cheehieu/recall/hw/docs/BLE/nRF52 Development Kit - Hardware files 1_1_1/PCA64110-NFC antenna flexprint 1_0_0/Production files/GERBER/400148_PCB_Laminate_Specification.pdf

### PCB Laminate Specification

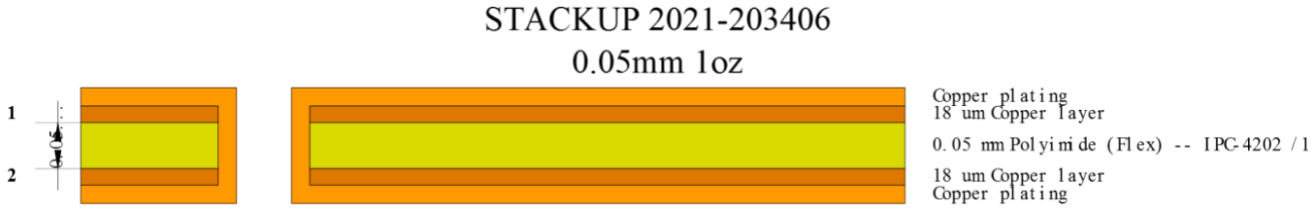
[picture p5: figure]

Page 1 of 1 | Rev. 1.0.0, 2016-03-10

PCB laminate parameters

PCB code | 4000148
Number of copper layers | 2 layers
Laminate material | FR4
Total board thickness | 0.05mm
PCB stackup | See Figure 1
Copper thickness | See Figure 1
Surface finish | Lead-Free HASL
Compliance with environmental directives | RoHS

Table 1: PCB substrate details

The PCB layer stackup order (from top layer and down) shall be as follows with reference to the Gerber file extensions given below:

- Top layer: | .GTL
- Bottom layer: | .GBL

Stackup

Figure 1: Elprint's 2 layer 2021-203406 stackup
