cheehieu/recall/docs/reminder.pdf

Product: Reminder

- All hardware
- Water proof
- Stupid cheap

Components:

- Transparent Silicon Rubber Button
- 555 timer or equivalent
- Low power LED
- Watch battery
- Sticky tape for mounting

Usage:

- Press button and an LED blinks lighting up button
- Blinks for 30 minutes or until pressed again
- Stick around the house, shower, etc.

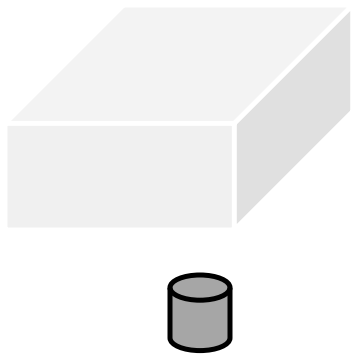
[picture p6: figure]

Silicon transparent button

Toggle button switch

Timer (and capacitor)

Low energy LEDs (on if bright enough)

Watch battery

Back plate

Sticky tape

Before press

After press for up to 30 minutes blinking
