cheehieu/recall/mech/recall_clip/recall_clip_male.step

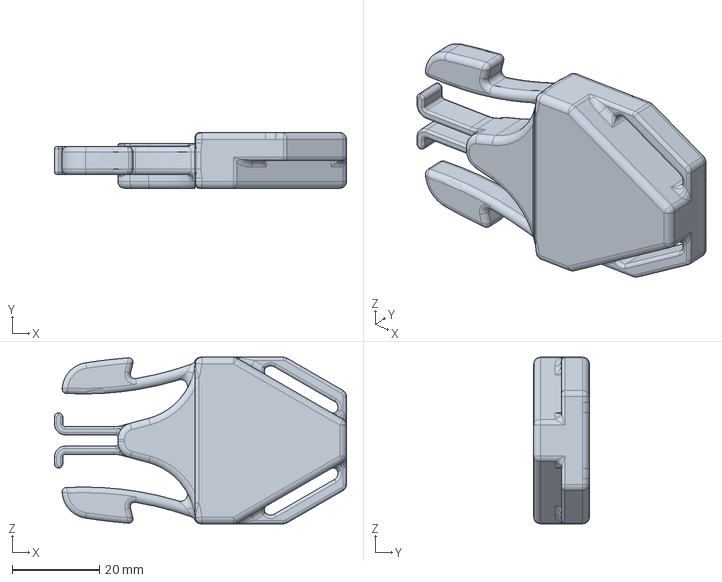
[picture p21: CAD file, 2016-09-16]
mech/recall_clip/recall_clip_male.step
66.8 x 12.7 x 38.1 mm
