cheehieu/recall/mech/recall_clip/bg_clip_female.step

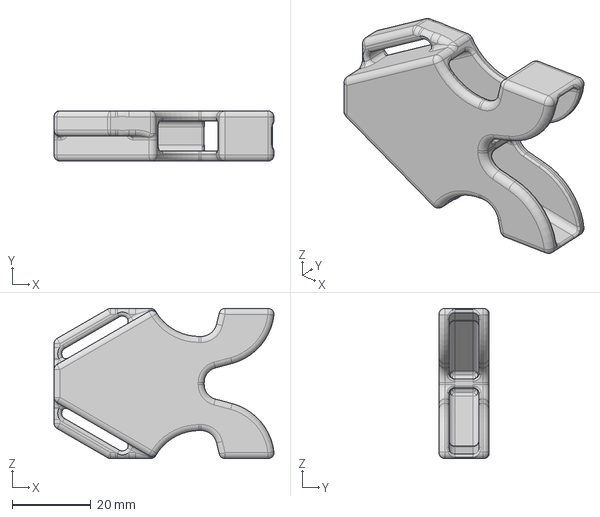
[picture p22: CAD file, 2016-09-16]
mech/recall_clip/bg_clip_female.step
55.8 x 12.7 x 38.1 mm
