cheehieu/recall/mech/recall_clip/recall_midplate.step

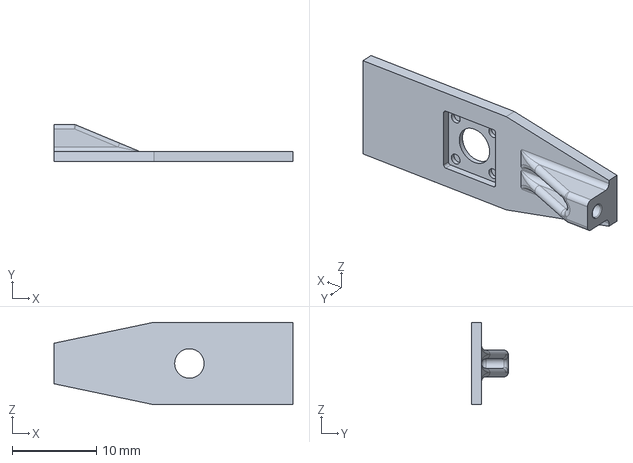
[picture p23: CAD file, 2016-09-16]
mech/recall_clip/recall_midplate.step
28.4 x 4.37 x 9.81 mm
