cheehieu/recall/mech/recall_clip/bg_clip_male.step

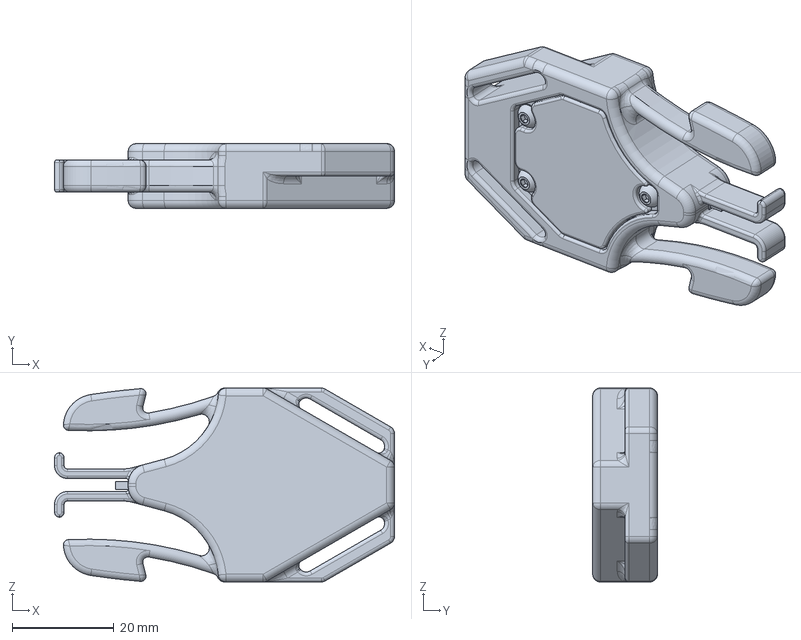
[picture p24: CAD file, 2016-09-16]
mech/recall_clip/bg_clip_male.step
66.8 x 12.7 x 38.1 mm
BG Clip Male 2.0 male
BG-switch
BG-board
BG Clip Male 2.0 mid plate
BG-Batt+holder
BG Clip Male 2.0 cover
92095A457 x 3
