cheehieu/recall/mech/recall_clip/bg_clip_midplate.stl

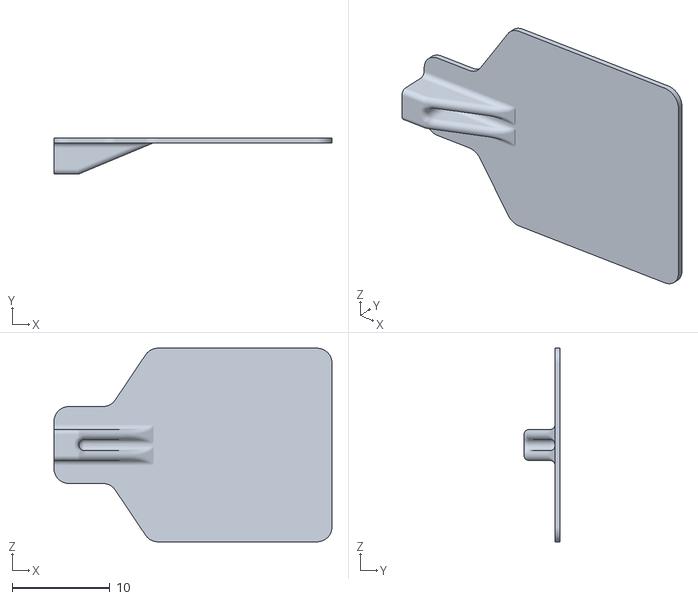
[picture p25: CAD file, 2016-09-09]
mech/recall_clip/bg_clip_midplate.stl
28.4 x 3.68 x 19.8
