cheehieu/recall/fw/recall_fw_v0_1/device_initialize.c

/****************************************************************************
;*	Microchip Technology Inc. 2007                                      *
;*	Assembler version:  XC8 v1.34                                       *
;*	Filename:                                                           *
;*		device_initilize.c                                                       *
;*	Dependents:                                                         *
;*                                                                          *
;*	April 13, 2015                                                      *
;*      PIC10(L)32X Developmental Board                                     *
;*      Demonstration program:                                              *
;*          After applying power to the PIC10(L)F32X Development Board,     *
;*          LED (D1) will automatically turn on.  Turn POT1 clockwise       *
;*          to increase the brightness of LED (D2).  Press switch (SW1)     *
;*          to turn both LEDs D1 and D2 off, release switch (SW1) and       *
;*          LEDs D1 and D2 will turn on.                                    *
;*                                                                          *
;****************************************************************************/

// Configuration Bits
#pragma config FOSC = INTOSC    // Oscillator Selection bits (INTOSC oscillator: CLKIN function disabled)
#pragma config BOREN = OFF      // Brown-out Reset Enable (Brown-out Reset disabled)
#pragma config WDTE = OFF       // Watchdog Timer Enable (WDT disabled)
#pragma config PWRTE = OFF      // Power-up Timer Enable bit (PWRT disabled)
#pragma config MCLRE = ON       // MCLR Pin Function Select bit (MCLR pin function is MCLR)
#pragma config CP = OFF         // Code Protection bit (Program memory code protection is disabled)
#pragma config LVP = ON         // Low-Voltage Programming Enable (Low-voltage programming enabled)
#pragma config LPBOR = OFF      // Brown-out Reset Selection bits (BOR disabled)
#pragma config BORV = LO        // Brown-out Reset Voltage Selection (Brown-out Reset Voltage (Vbor), low trip point selected.)
#pragma config WRT = OFF        // Flash Memory Self-Write Protection (Write protection off)

#include "device_initialize.h"

void SYSTEM_Initialize(void)
{
    OSCILLATOR_Initialize();
    TMR2_Initialize();
}

void OSCILLATOR_Initialize(void)
{
    OSCCON = 0x00;  //31kHz LFINTOSC
}

// End of File
